tweilu/6.s079-musicbox/Code/Comb/dynspace_base.dxf

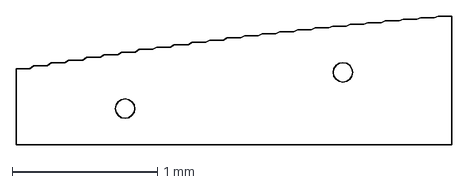
[picture p29: CAD file, 2015-05-02]
Code/Comb/dynspace_base.dxf
3.00 x 0.887 mm
