tweilu/6.s079-musicbox/Code/Comb/comb.dxf

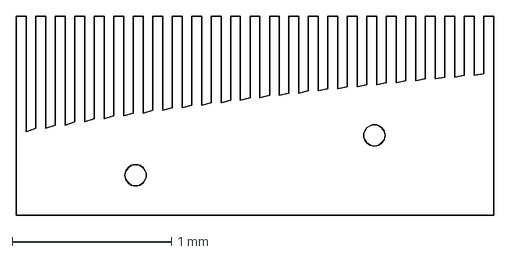
[picture p30: CAD file, 2015-05-02]
Code/Comb/comb.dxf
3.00 x 1.25 mm
