tweilu/6.s079-musicbox/Code/Comb/dynspace_comb.dxf

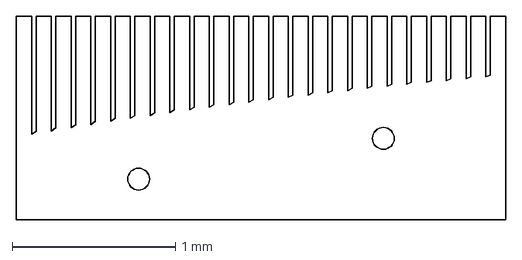
[picture p31: CAD file, 2015-05-02]
Code/Comb/dynspace_comb.dxf
3.00 x 1.25 mm
