tweilu/6.s079-musicbox/Code/Comb/base.dxf

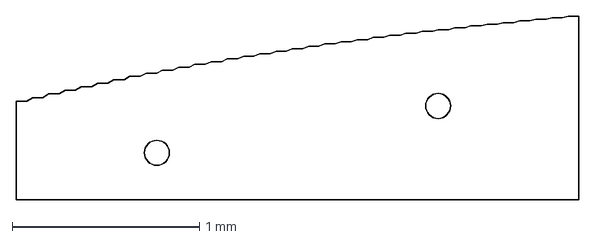
[picture p32: CAD file, 2015-04-26]
Code/Comb/base.dxf
3.00 x 0.978 mm
